poppy-project/Poppy-eva-head-design/doc/img/all.jpg

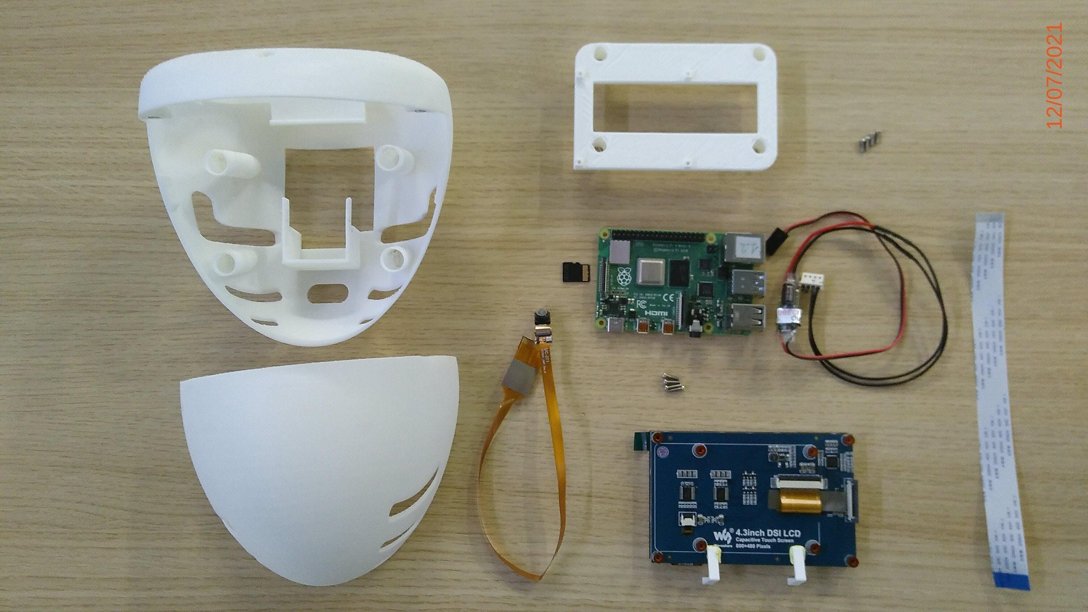
doc/img/all.jpg
